eMakerspace/barbot/esp32/barbotv2/src/tasks/serial.rs

use embedded_io_async::Read;
use esp_hal::usb_serial_jtag::UsbSerialJtagRx;
use esp_println::print;
use num_traits::ToPrimitive;
use num_traits::float::FloatCore;

use crate::cmd::{Cmd, CmdChannel, StepperCmd, StopCmd, StopCmdPub};
use crate::stepper::AccelSpeedConfig;

/// Read from the USB serial and execute the commands
#[embassy_executor::task]
pub async fn serial_reader(
    mut rx: UsbSerialJtagRx<'static, esp_hal::Async>,
    cmd_chan: &'static CmdChannel,
    stop_pub: StopCmdPub,
) {
    let mut buf = [0_u8; 128];

    let mut total_read: usize = 0;
    let mut ignore_next_command = false;
    let mut should_echo = true;
    loop {
        let count_read = match rx.read(&mut buf[total_read..]).await {
            Err(err) => {
                log::error!("{err}");
                continue;
            }
            Ok(val) => val,
        };

        // Echo.
        if should_echo {
            esp_println::Printer::write_bytes(&buf[total_read..total_read + count_read]);
        }

        if let Some((idx, c)) = buf[total_read..total_read + count_read]
            .iter()
            .enumerate()
            .find(|(_i, c)| **c == b'\r' || **c == b'\n')
        {
            if should_echo {
                // Echo the appropriate missing character so that we echo a CRLF or LFCR,
                // for a true linebreak.
                if *c == b'\n' {
                    print!("\r");
                } else if total_read + idx + 1 == total_read + count_read {
                    print!("\n");
                }
            }

            total_read += idx;
            let s = match core::str::from_utf8(&buf[..total_read]) {
                Ok(s) => s,
                Err(_) => {
                    log::warn!("invalid utf-8 received");
                    continue;
                }
            };

            if !ignore_next_command {
                handle_cmd(s.trim(), cmd_chan, &mut should_echo, &stop_pub).await;
            }
            ignore_next_command = false;

            let range_start = total_read + 1;
            let range_end = total_read - idx + count_read;
            buf.copy_within(range_start..range_end, 0);
            total_read = count_read - idx - 1;
        } else {
            total_read += count_read;
        }

        if total_read == buf.len() {
            log::warn!("ignoring command, buffer full");
            total_read = 0;
            ignore_next_command = true;
        }
    }
}

fn parse_optional_accel_config(
    gcmd: &gcode::GCode,
) -> Option<AccelSpeedConfig> {
    let accel_opt = gcmd.value_for('A');
    let speed_opt = gcmd.value_for('S');

    // If neither parameter is provided, use None to signal default config
    if accel_opt.is_none() && speed_opt.is_none() {
        return None;
    }

    // Use global defaults for whichever parameter is not provided
    let accel_full_steps = accel_opt.unwrap_or(3000.0) as f64;
    let speed_full_steps = speed_opt.unwrap_or(4000.0) as f64;

    // Convert from full steps to microsteps and build config
    let config = AccelSpeedConfig::zero()
        .with_acceleration(accel_full_steps * crate::MICROSTEPS)
        .with_max_speed(speed_full_steps * crate::MICROSTEPS);

    Some(config)
}

async fn handle_cmd(
    cmd: &str,
    cmd_chan: &'static CmdChannel,
    should_echo: &mut bool,
    stop_pub: &StopCmdPub,
) {
    let gcmd = match gcode::parse(cmd).next() {
        Some(cmd) => cmd,
        None => {
            log::warn!("received cmd '{cmd}' is not valid gcode");
            return;
        }
    };

    let invalid_cmd = || {
        log::error!("invalid command \"{gcmd}\"\r");
    };

    let invalid_cmd_msg = |msg: &str| {
        log::error!("invalid command \"{gcmd}\": {msg}\r");
    };

    match gcmd.mnemonic() {
        gcode::Mnemonic::General => match gcmd.major_number() {
            // `G0.1 X{range_fact} [A{accel}] [S{speed}]` for moving the stepper motor to `range_fact * end_step`.
            0 if gcmd.minor_number() == 1 => {
                let Some(range_fact) = gcmd.value_for('X') else {
                    invalid_cmd_msg("missing X parameter");
                    return;
                };
                if range_fact < 0.0 || range_fact > 1.0 {
                    invalid_cmd_msg("X parameter out of range");
                    return;
                }
                let accel_cfg = parse_optional_accel_config(&gcmd);
                cmd_chan
                    .send(Cmd::Stepper(StepperCmd::GoToRangeFact(range_fact, accel_cfg)))
                    .await;
            }
            // `G0 X{position} [A{accel}] [S{speed}]` Move stepper motor to step {position}.
            0 => {
                if let Some(loc) = gcmd.value_for('X') {
                    let Some(loc) = (loc * crate::MICROSTEPS as f32).round().to_i32() else {
                        invalid_cmd_msg("X parameter out of range");
                        return;
                    };

                    let accel_cfg = parse_optional_accel_config(&gcmd);
                    cmd_chan.send(Cmd::Stepper(StepperCmd::GoTo(loc, accel_cfg))).await;
                } else {
                    invalid_cmd_msg("missing X parameter");
                    return;
                }
            }
            // `G1 Z{angle}` to move servo to angle (0–180 degrees).
            1 => {
                let Some(angle) = gcmd.value_for('Z') else {
                    invalid_cmd_msg("missing Z<angle> parameter (0-180)");
                    return;
                };
                let angle = angle.round();
                if angle < 0.0 || angle > 180.0 {
                    invalid_cmd_msg("Z angle out of range (0-180)");
                    return;
                }
                cmd_chan
                    .send(Cmd::Servo(crate::cmd::ServoCmd { angle: angle as u8 }))
                    .await;
            }
            // `G5 P{slot4_pos} Q{slot5_pos}` — set forbidden zone slot positions.
            // The Pi sends this at boot so the ESP32 can compute the danger zone.
            5 => {
                let Some(p4) = gcmd.value_for('P') else {
                    invalid_cmd_msg("missing P<slot4_pos> parameter");
                    return;
                };
                let Some(p5) = gcmd.value_for('Q') else {
                    invalid_cmd_msg("missing Q<slot5_pos> parameter");
                    return;
                };
                let p4 = (p4 * crate::MICROSTEPS as f32).round() as i32;
                let p5 = (p5 * crate::MICROSTEPS as f32).round() as i32;
                crate::SLOT4_POS.store(p4, portable_atomic::Ordering::Relaxed);
                crate::SLOT5_POS.store(p5, portable_atomic::Ordering::Relaxed);
                log::info!("Forbidden zone set: slot4={} slot5={} (buffer={})\r",
                    p4, p5, crate::SERVO_ZONE_BUFFER);
            }
            // `G28` start homing.
            28 => {
                cmd_chan.send(Cmd::Stepper(StepperCmd::Home())).await;
            }
            _ => invalid_cmd(),
        },
        gcode::Mnemonic::Miscellaneous => match gcmd.major_number() {
            // Stop the stepper motor.
            // - `M0.1` stops immediately.
            0 if gcmd.minor_number() == 1 => {
                stop_pub.publish_immediate(StopCmd::Immediate);
                log::info!("Stopping immediately from command");
            }
            // - `M0` stops slowly.
            0 => {
                stop_pub.publish(StopCmd::Graceful).await;
                log::info!("Stopping early from command");
            }
            // `M1` recovers from stop.
            1 => {
                stop_pub.publish(StopCmd::Continue).await;
                log::info!("Continuing from stop command");
            }
            // `M10` Toggle local echo.
            10 => {
                *should_echo = !*should_echo;
            }
            // `M50` Query cup presence state.
            50 => {
                let cup_present = crate::CUP_PRESENT.load(portable_atomic::Ordering::Relaxed);
                if cup_present == 1 {
                    log::info!("[cup] PRESENT\r");
                } else {
                    log::info!("[cup] ABSENT\r");
                }
            }
            // `M`
            _ => invalid_cmd(),
        },
        gcode::Mnemonic::ToolChange => match gcmd.major_number() {
            // `T0 D{time_ms}` Wait for {time_ms} milliseconds.
            0 => {
                let Some(time_ms) = gcmd.value_for('D') else {
                    invalid_cmd_msg("missing D<time_ms> parameter");
                    return;
                };
                let Some(time_ms) = time_ms.round().to_u32() else {
                    invalid_cmd_msg("D parameter out of range");
                    return;
                };
                cmd_chan.send(Cmd::Wait(time_ms)).await;
            }
            _ => invalid_cmd(),
        },
        _ => invalid_cmd(),
    }
}
