eMakerspace/barbot/python_script2/orders.py

"""Order polling, parsing, and processing."""

import threading
import time

from config import BarbotConfig, AttributesConfig
from store import StoreConfig
from woo_client import WooClient
from hardware import HardwareInterface
from mixer import DrinkResolver
from progress import OrderProgress
from logger import log_debug, log_info, log_warn, log_error

HEARTBEAT_INTERVAL = 15  # seconds between heartbeats during mixing


class OrderProcessor:
    """Fetches, parses, and executes WooCommerce orders."""

    def __init__(
        self,
        config: BarbotConfig,
        store: StoreConfig,
        attributes: AttributesConfig,
        woo: WooClient,
        hardware: HardwareInterface,
        ui=None,  # LCDMenu reference, injected after construction to avoid circular import
    ):
        self.config = config
        self.store = store
        self.attributes = attributes
        self.woo = woo
        self.hw = hardware
        self.ui = ui
        self.resolver = DrinkResolver(config, store, attributes)
        self.progress = OrderProgress()
        self._heartbeat_stop = threading.Event()

    def _heartbeat_thread(self):
        """Send heartbeats at a fixed interval until _heartbeat_stop is set."""
        log_debug("ORDER", "Heartbeat thread started")
        while not self._heartbeat_stop.wait(HEARTBEAT_INTERVAL):
            self.woo.send_heartbeat()
        log_debug("ORDER", "Heartbeat thread stopped")

    def _start_heartbeat(self):
        self._heartbeat_stop.clear()
        t = threading.Thread(target=self._heartbeat_thread, daemon=True)
        t.start()
        log_debug("ORDER", "Heartbeat thread started")
        return t

    def _stop_heartbeat(self, thread: threading.Thread):
        log_debug("ORDER", "Stopping heartbeat thread...")
        self._heartbeat_stop.set()
        thread.join(timeout=HEARTBEAT_INTERVAL + 5)
        log_debug("ORDER", "Heartbeat thread stopped")

    def process_order(self, order: dict):
        """Parse all line items, make each drink, then mark order completed.

        Args:
            order: WooCommerce order dict
        """
        order_id = order["id"]
        short_id = order_id % 100
        line_items = order.get("line_items", [])

        # Expand all line items into an ordered flat list of DrinkSpecs
        all_specs = []
        for item in line_items:
            all_specs.extend(self.resolver.resolve(item))

        total = len(all_specs)
        log_info("ORDER", f"Order #{order_id}: {total} drink(s) in {len(line_items)} line item(s)")

        # Check for saved progress from a previous interrupted run
        skip = self.progress.resume_from_disk(order_id, total)
        if skip == 0:
            self.progress.start(order_id, total)
        elif skip > 0:
            log_info("ORDER", f"Order #{order_id}: Resuming from drink {skip}/{total}")

        self.hw.display_order_id(short_id)

        # Keep sending heartbeats while mixing so the website doesn't lock up
        hb_thread = self._start_heartbeat()
        try:
            for drink_num, spec in enumerate(all_specs, start=1):
                if drink_num <= skip:
                    log_debug("ORDER", f"Order #{order_id}: Skipping drink {drink_num}/{total} (already made)")
                    continue

                log_info("ORDER", f"Order #{order_id}: Making drink {drink_num}/{total}: {spec.name}")
                spec.log()

                while True:  # Retry loop for this drink
                    try:
                        if self.ui:
                            self.ui.show_mixing(drink_num, total, spec.name)
                        self.hw.make_drink(spec)
                        self.progress.drink_done()
                        if self.ui:
                            self.ui.show_drink_finished()
                        self.hw.wait_for_cup_removal()  # Success: wait for cup removal
                        break  # Success — exit retry loop
                    except Exception as e:
                        log_error("ORDER", f"Order #{order_id}: Error making drink: {e}")
                        if self.ui:
                            self.ui.clear_mixing()
                            # Show red flash error animation while waiting for user choice
                            if self.hw._neo:
                                self.hw._neo.send("-e RED_FLASH_FAST")
                            self.ui.pause_polling(f"Drink {drink_num}: {str(e)[:20]}")
                            # Wait for user to confirm their choice via LCD
                            with self.ui._pause_cv:
                                while self.ui._polling_paused:
                                    self.ui._pause_cv.wait()
                                should_retry = self.ui._retry_drink
                            # Show "replace failed drink" and wait for removal
                            if self.ui:
                                self.ui.show_replace_failed_drink()
                            self.hw.wait_for_cup_removal(is_failed=True)
                            # After cup is removed, force the next wait_for_cup() to require a fresh placement
                            self.hw.force_require_cup_removal()
                            if should_retry:
                                log_info("ORDER", f"Order #{order_id}: User chose RETRY for drink {drink_num}")
                                continue  # Retry this drink
                            else:
                                log_info("ORDER", f"Order #{order_id}: User chose CANCEL for drink {drink_num}")
                                self.progress.drink_done()  # Mark as done to move progress forward
                                break  # Skip to next drink
                        else:
                            # No UI — re-raise so polling thread can handle it
                            raise
        finally:
            self._stop_heartbeat(hb_thread)

        if self.ui:
            self.ui.clear_mixing()
        self.progress.clear()
        self.woo.update_order_status(order_id, "completed")
        log_info("ORDER", f"Order #{order_id}: Completed and status set to completed")

    def skip_current_drink(self):
        """Advance progress past the currently-failed drink without making it."""
        self.progress.drink_done()
